PaddyCube/WirelessWeather/Pictures/20190723_202139.jpg

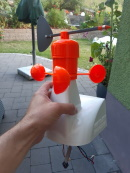
Pictures/20190723_202139.jpg
