PaddyCube/WirelessWeather/Pictures/20190723_202154.jpg

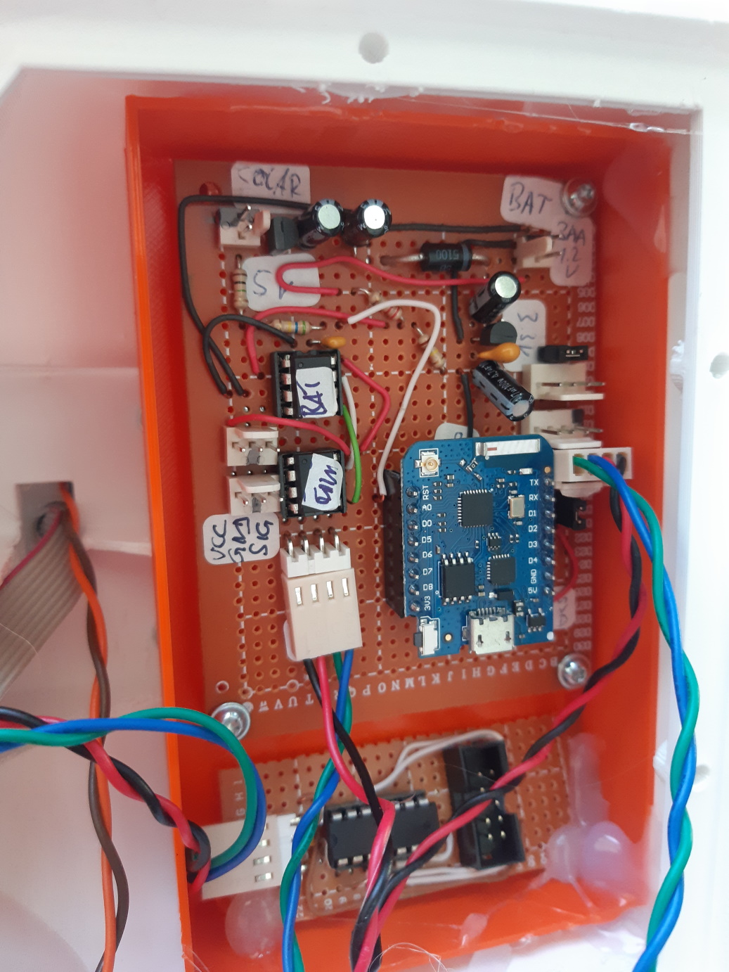
Pictures/20190723_202154.jpg
