PaddyCube/WirelessWeather/Pictures/20190723_202201.jpg

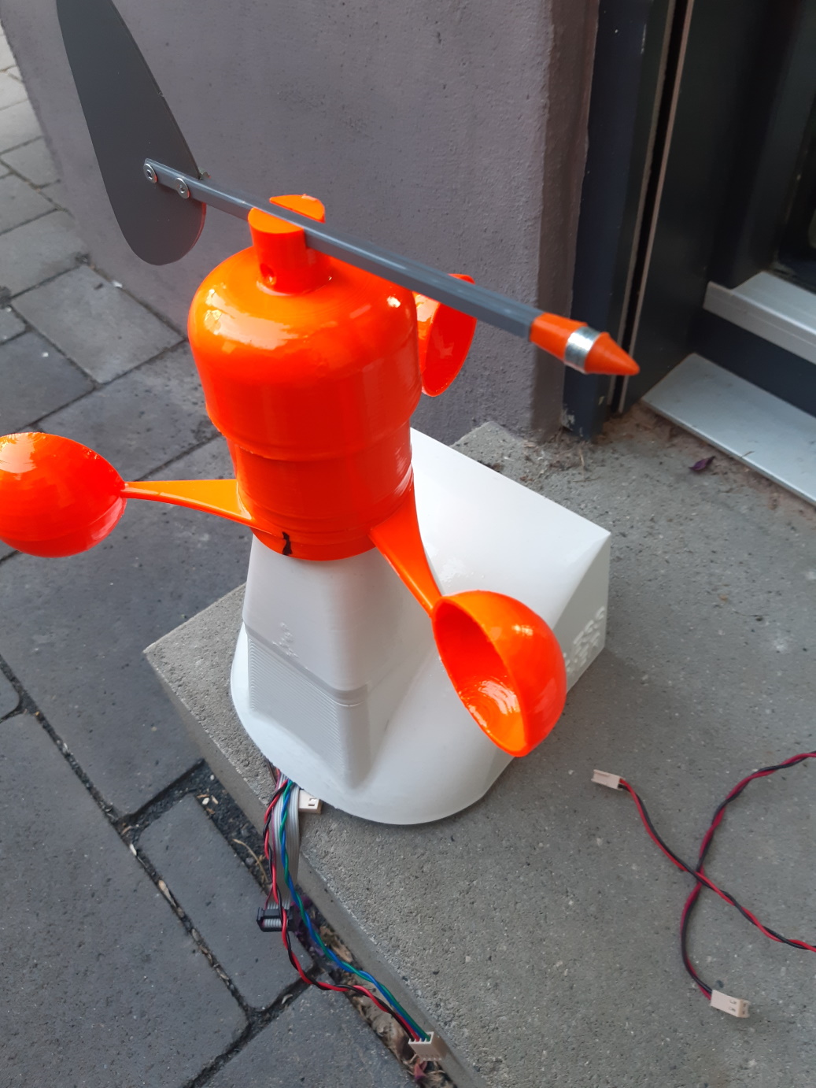
Pictures/20190723_202201.jpg
