PaddyCube/WirelessWeather/Pictures/20190723_202206.jpg

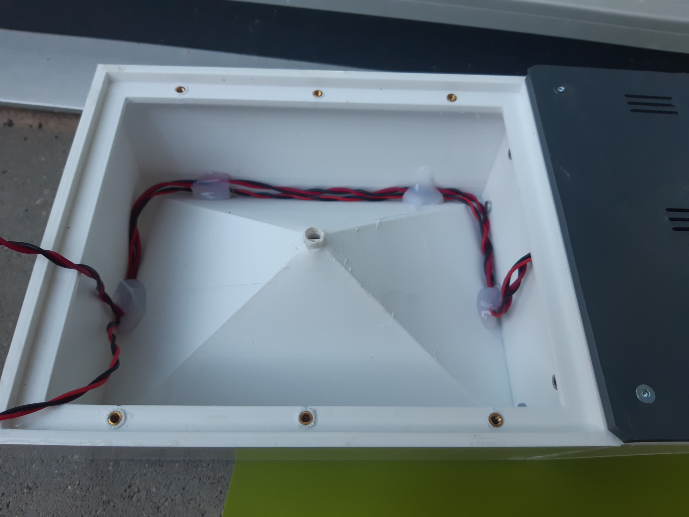
Pictures/20190723_202206.jpg
