PaddyCube/WirelessWeather/Pictures/20190723_202212.jpg

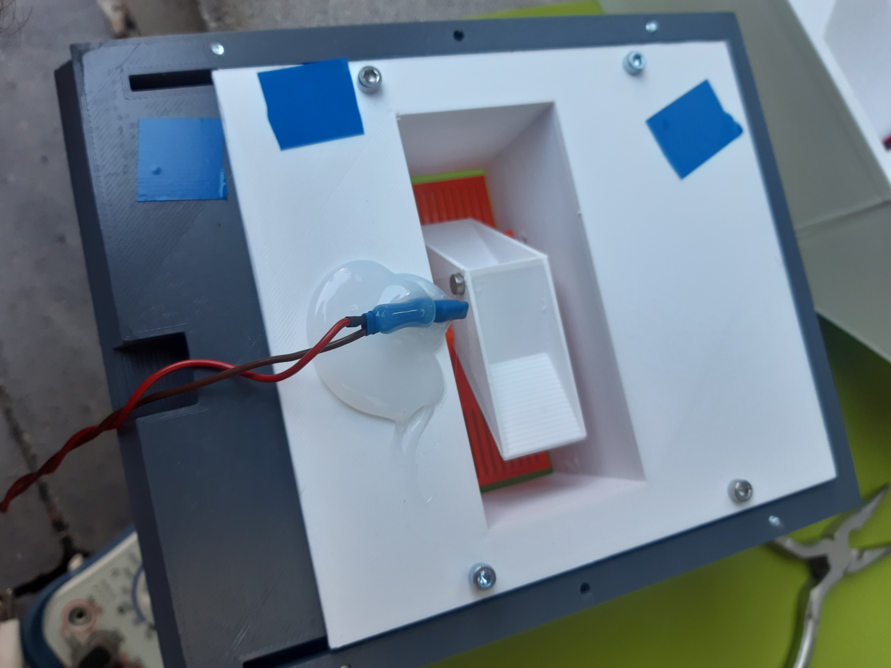
Pictures/20190723_202212.jpg
