PaddyCube/WirelessWeather/Pictures/20190723_202252.jpg

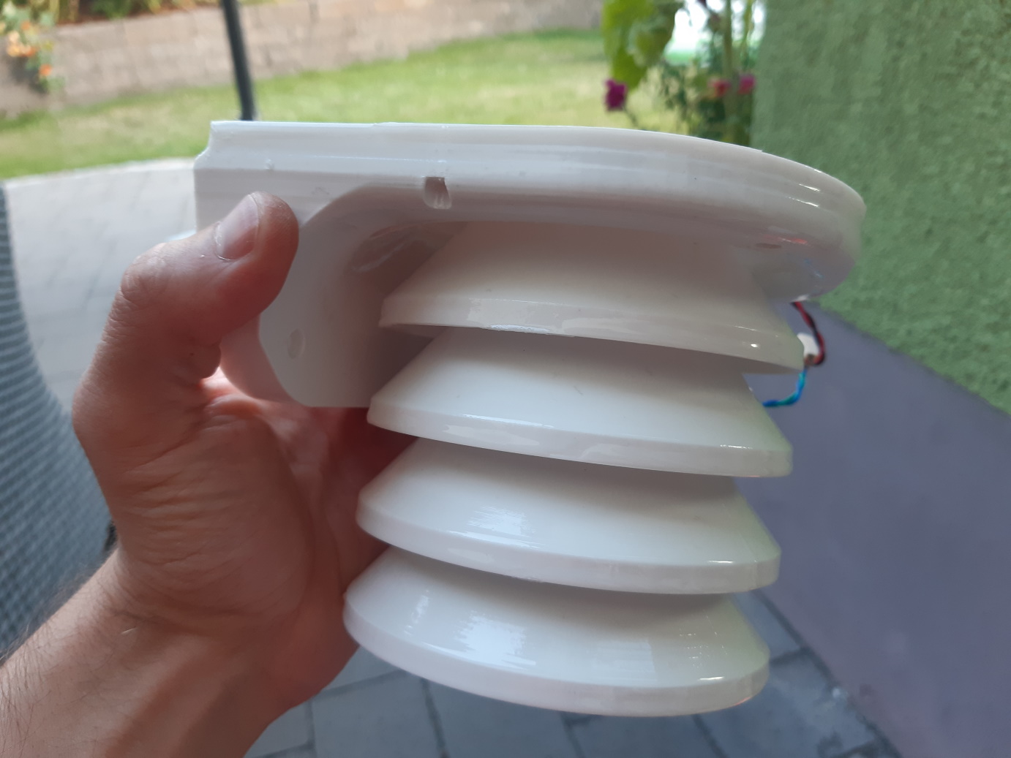
Pictures/20190723_202252.jpg
