PaddyCube/WirelessWeather/Pictures/20190723_202256.jpg

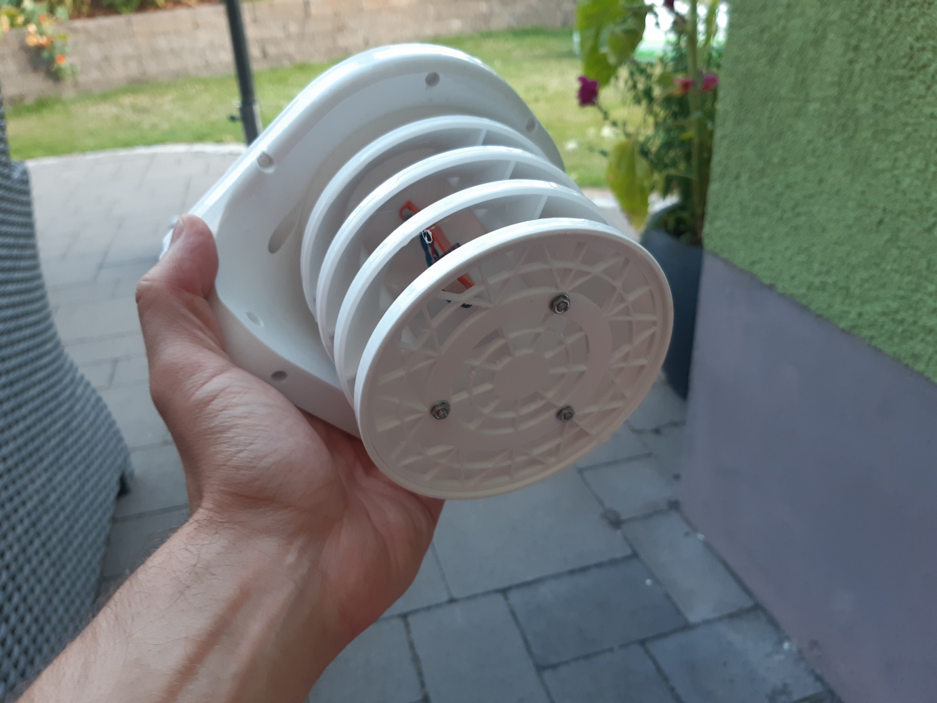
Pictures/20190723_202256.jpg
