PaddyCube/WirelessWeather/Pictures/20190803_131221.jpg

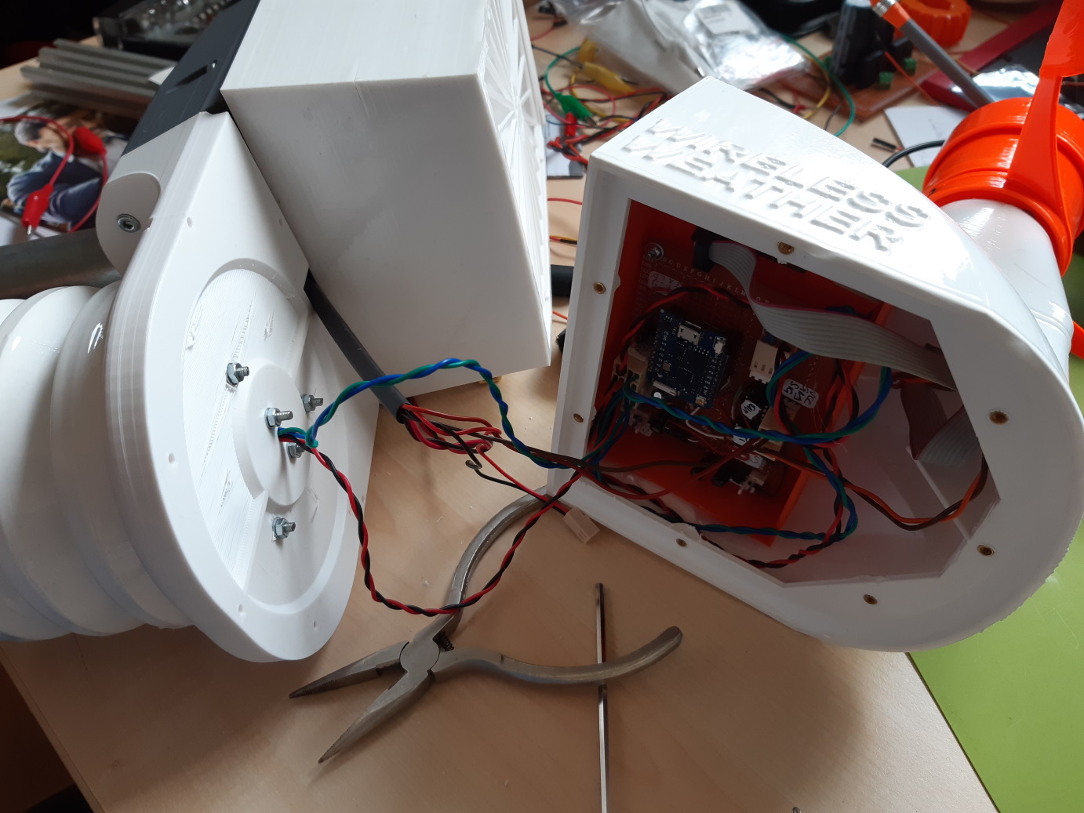
Pictures/20190803_131221.jpg
