PaddyCube/WirelessWeather/Pictures/20190803_132253.jpg

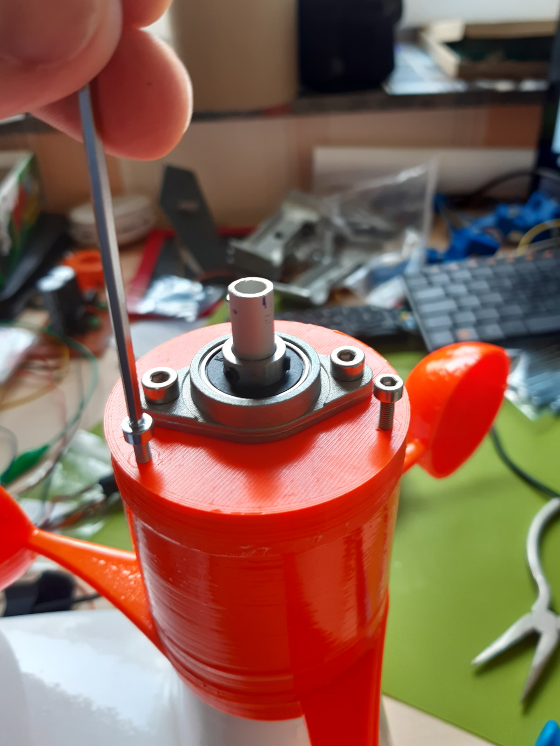
Pictures/20190803_132253.jpg
