PaddyCube/WirelessWeather/Pictures/20190803_132257.jpg

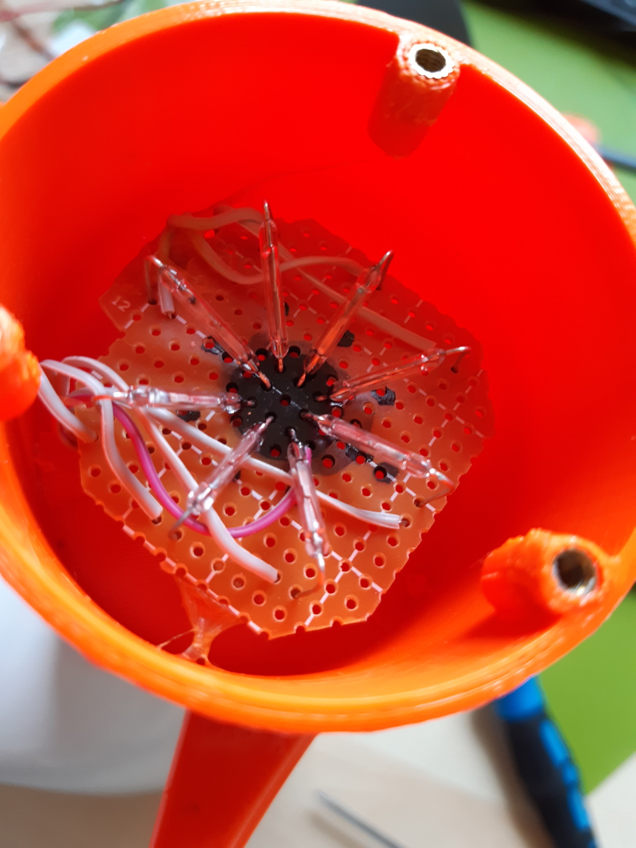
Pictures/20190803_132257.jpg
