PaddyCube/WirelessWeather/Pictures/20190806_172404.jpg

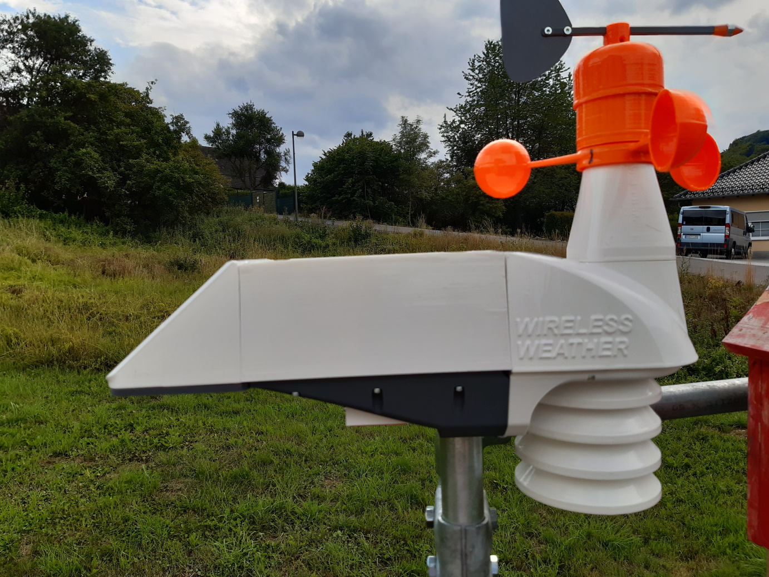
Pictures/20190806_172404.jpg
