PaddyCube/WirelessWeather/Pictures/20190806_172607.jpg

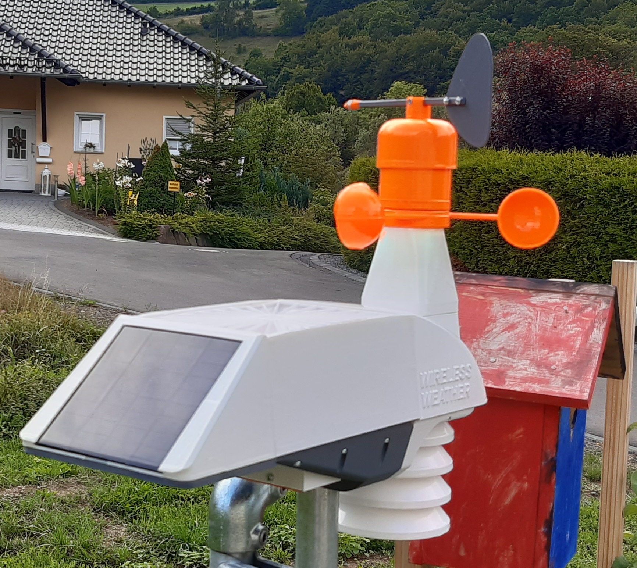
Pictures/20190806_172607.jpg
