PaddyCube/WirelessWeather/STL/schnitt.png

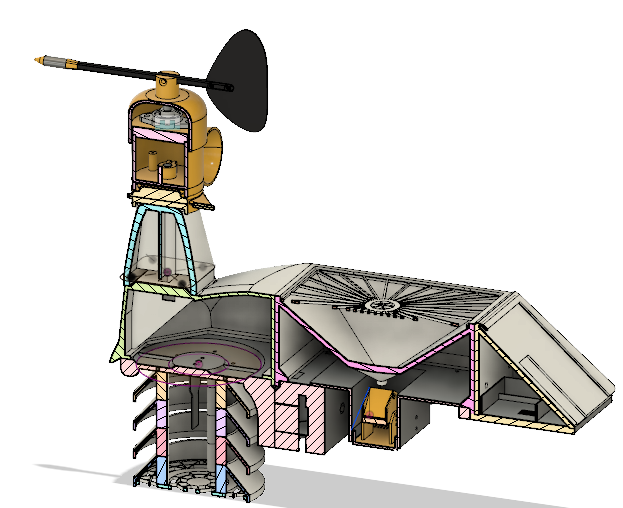
STL/schnitt.png
