PaddyCube/WirelessWeather/STL/seite.png

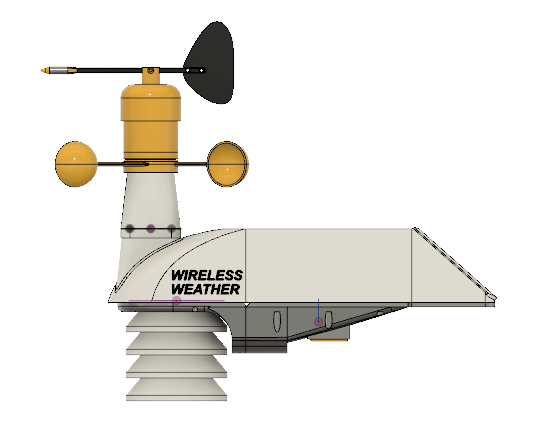
STL/seite.png
