PaddyCube/WirelessWeather/STL/station.png

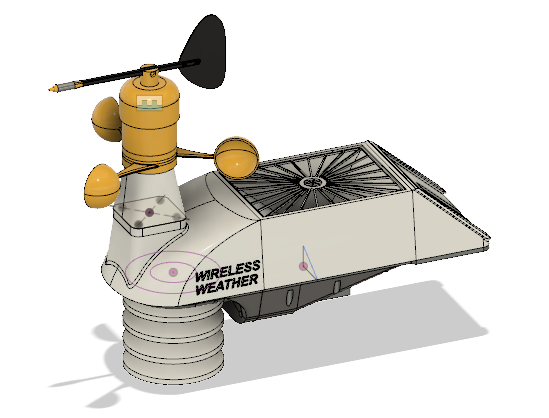
STL/station.png
