PaddyCube/WirelessWeather/STL/unten.png

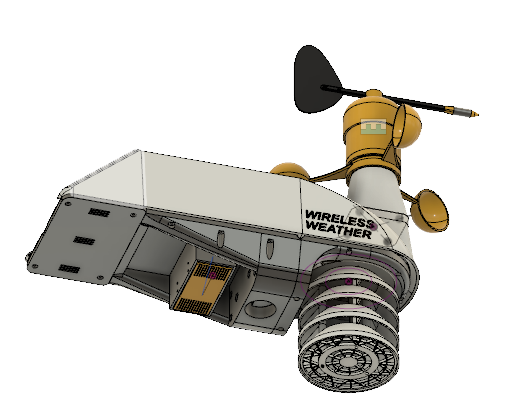
STL/unten.png
