PaddyCube/WirelessWeather/STL/vorne.png

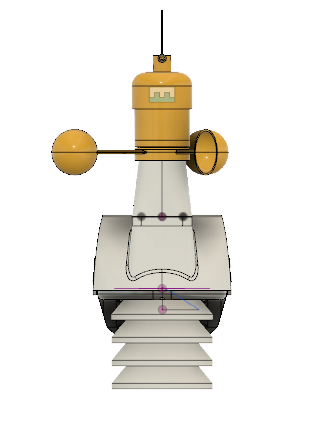
STL/vorne.png
