PaddyCube/WirelessWeather/STL/Anemometer-lower-part v17.stl

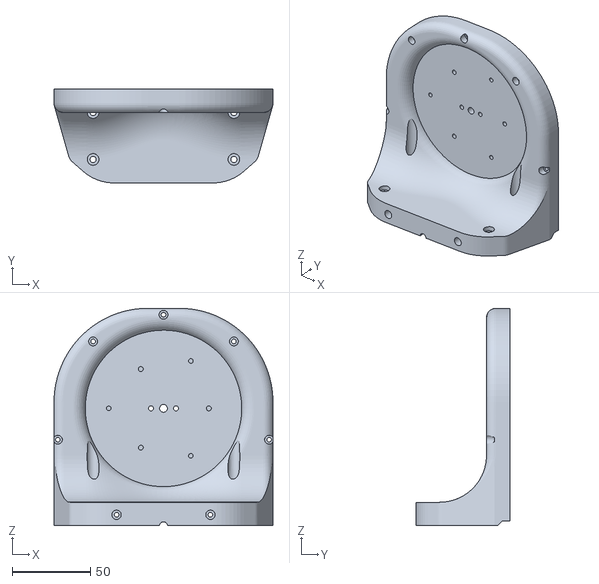
[picture p34: CAD file, 2020-04-20]
STL/Anemometer-lower-part v17.stl
140.0 x 60.0 x 139.0
