PaddyCube/WirelessWeather/STL/Sensor-Mount.stl

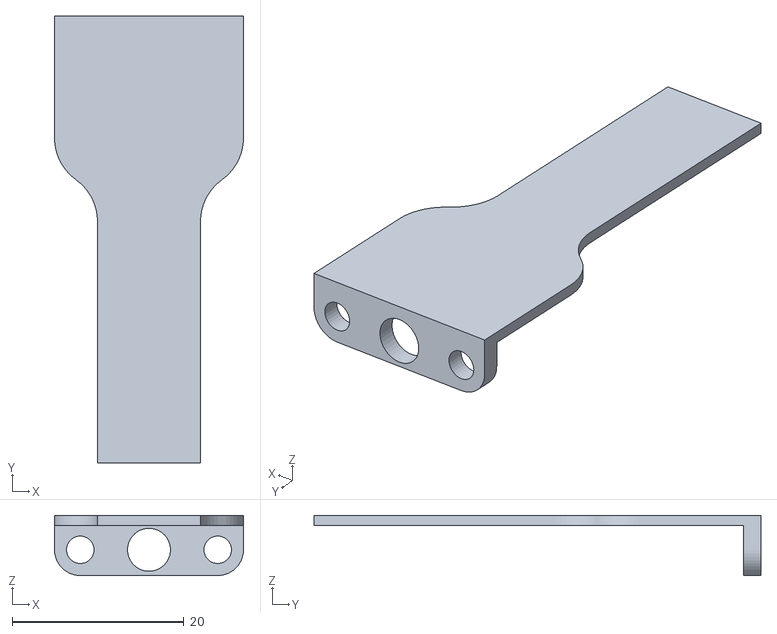
[picture p35: CAD file, 2020-04-20]
STL/Sensor-Mount.stl
22.0 x 52.0 x 7.00
