PaddyCube/WirelessWeather/STL/Rain_Gauge_Cover.stl

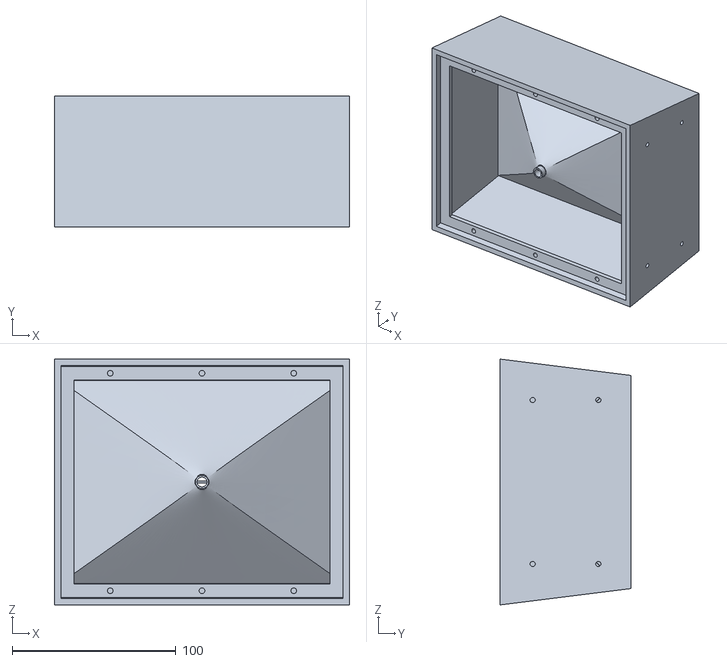
[picture p36: CAD file, 2020-04-20]
STL/Rain_Gauge_Cover.stl
180.0 x 80.0 x 150.0
