PaddyCube/WirelessWeather/STL/Solar-Modul.stl

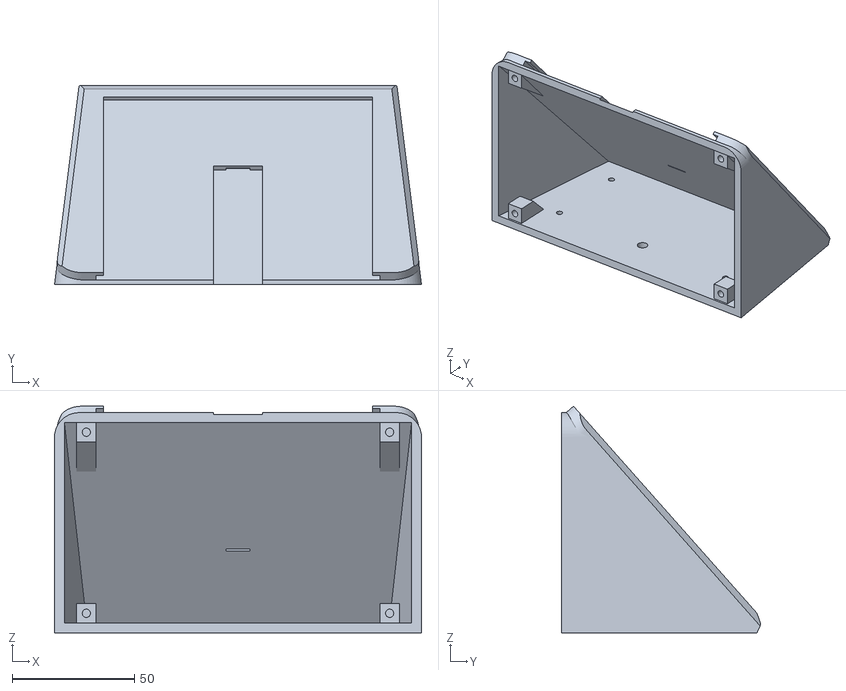
[picture p37: CAD file, 2020-04-20]
STL/Solar-Modul.stl
150.0 x 81.5 x 92.7
