PaddyCube/WirelessWeather/STL/Stevenson-Screen-Mittelteil.stl

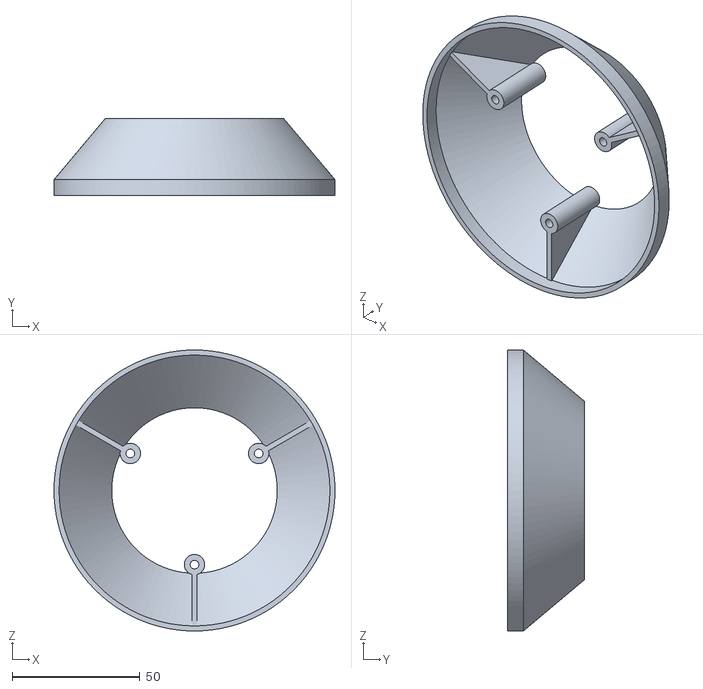
[picture p38: CAD file, 2020-04-20]
STL/Stevenson-Screen-Mittelteil.stl
110.0 x 30.0 x 110.0
