PaddyCube/WirelessWeather/STL/Wetterstation-upper-part.stl

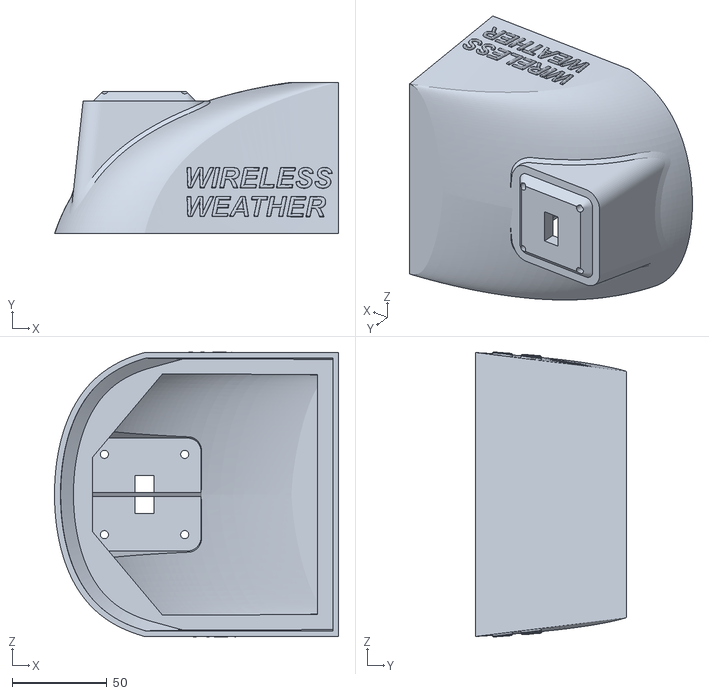
[picture p39: CAD file, 2020-04-20]
STL/Wetterstation-upper-part.stl
150.0 x 80.0 x 150.5
