PaddyCube/WirelessWeather/STL/Windfahne-unten.stl

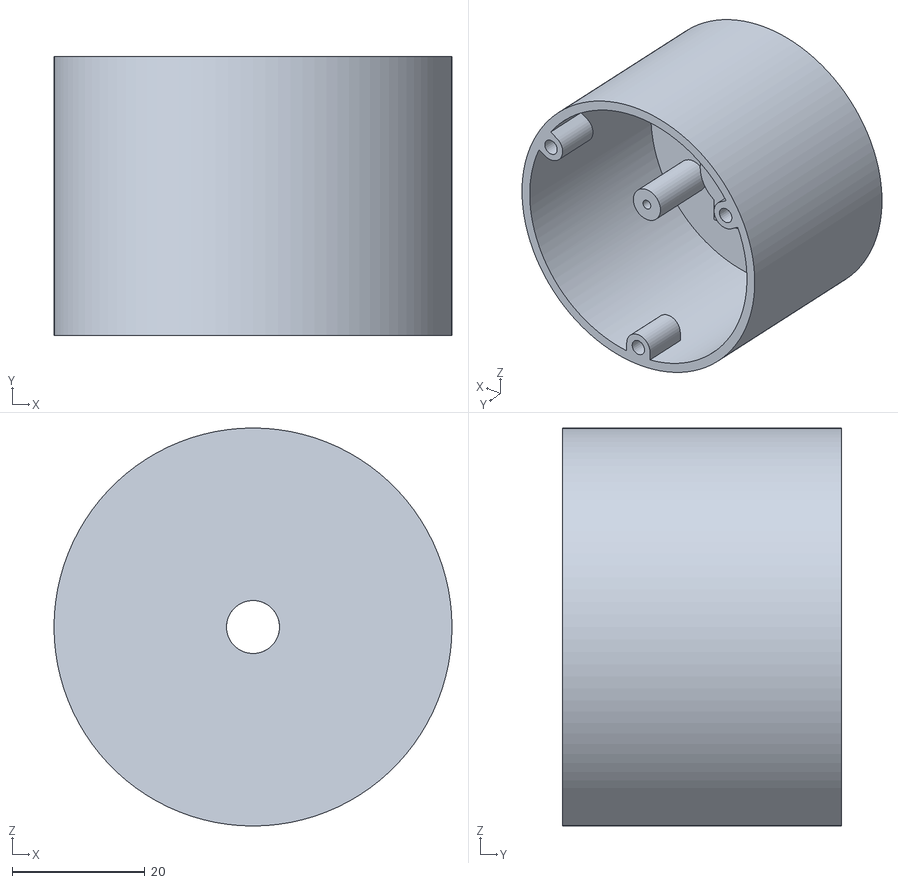
[picture p40: CAD file, 2020-04-20]
STL/Windfahne-unten.stl
60.0 x 42.0 x 60.0
