PaddyCube/WirelessWeather/STL/Windfahne-Balance1.stl

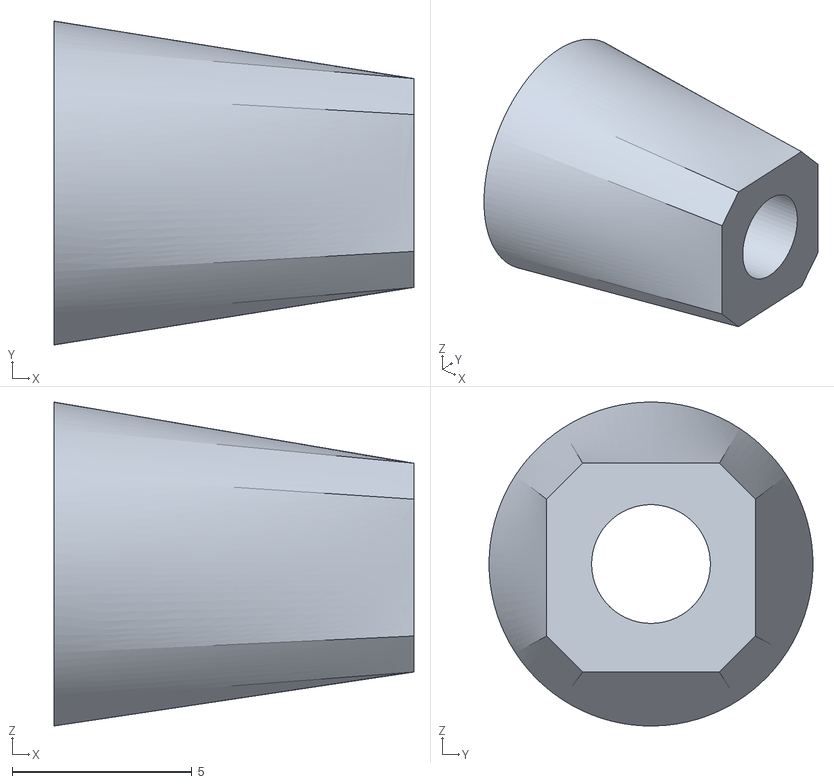
[picture p41: CAD file, 2020-04-20]
STL/Windfahne-Balance1.stl
10.0 x 9.00 x 9.00
