PaddyCube/WirelessWeather/STL/Windfahne-Mast.stl

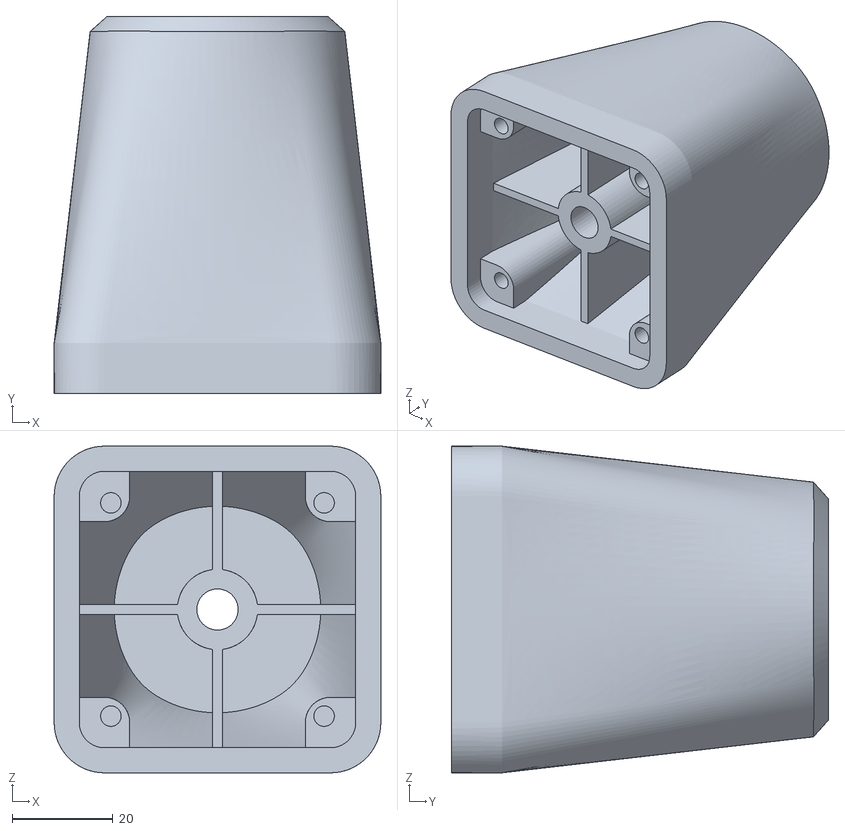
[picture p42: CAD file, 2020-04-20]
STL/Windfahne-Mast.stl
65.0 x 75.0 x 65.0
