PaddyCube/WirelessWeather/STL/Windfahne-Deckel.stl

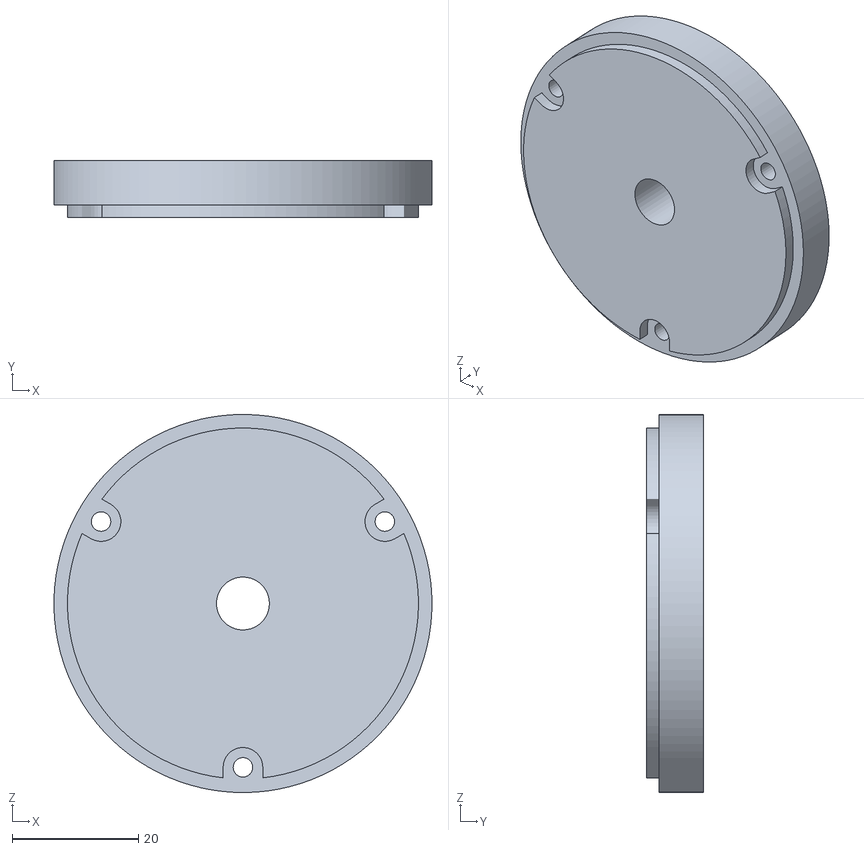
[picture p43: CAD file, 2020-04-20]
STL/Windfahne-Deckel.stl
60.0 x 9.00 x 60.0
