PaddyCube/WirelessWeather/STL/Windfahne-Paddel.stl

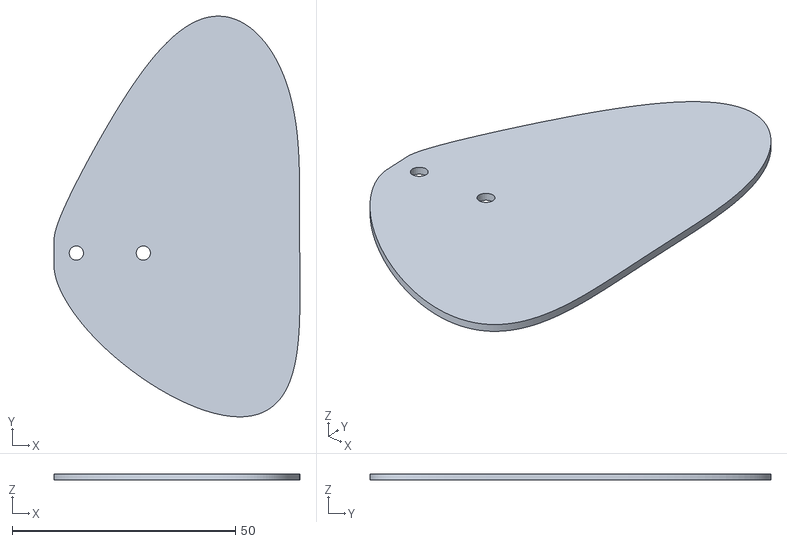
[picture p44: CAD file, 2020-04-20]
STL/Windfahne-Paddel.stl
55.1 x 89.7 x 1.40
