PaddyCube/WirelessWeather/STL/Platinenhalter.stl

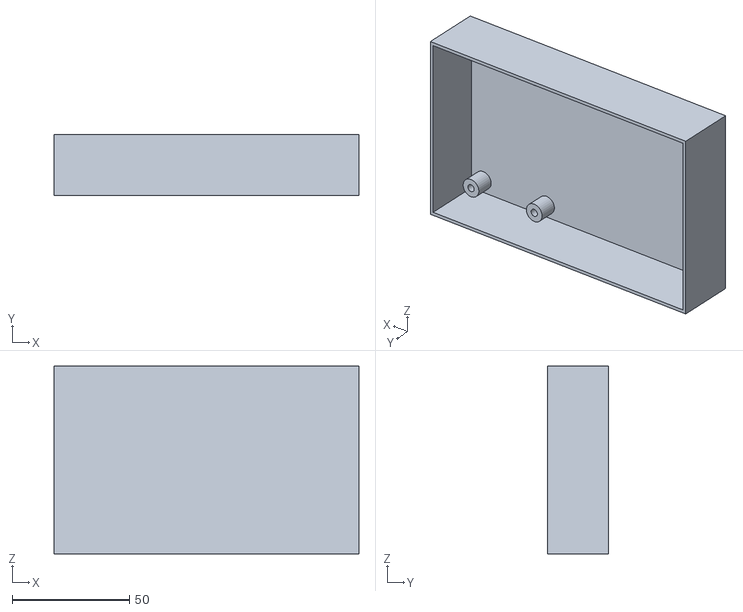
[picture p45: CAD file, 2020-04-20]
STL/Platinenhalter.stl
130.0 x 26.0 x 80.0
