PaddyCube/WirelessWeather/code/ESP32/ESP32_WirelessWeather/ulp_main.h

/*
    Put your ULP globals here you want visibility
    for your sketch. Add "ulp_" to the beginning
    of the variable name and must be size 'uint32_t'
*/
#include "Arduino.h"

extern uint32_t ulp_entry;

extern uint32_t ulp_edge_count_to_wake_up;
extern uint32_t ulp_debounce_max_count;

extern uint32_t ulp_next_edge_wind;
extern uint32_t ulp_debounce_counter_wind;
extern uint32_t ulp_edge_count_wind;
extern uint32_t ulp_io_number_wind;

extern uint32_t ulp_next_edge_rain;
extern uint32_t ulp_debounce_counter_rain;
extern uint32_t ulp_edge_count_rain;
extern uint32_t ulp_io_number_rain;
