PaddyCube/WirelessWeather/code/Arduino Mini/ESP8266WirelessWeatherReceiver/settings.h

#ifndef SETTINGS_H_
#define SETTINGS_H_


// WIFI -settings
const char *SSID = "YOUR SSID";
const char *PSK = "YOUR_PASSWORD";


// MQTT Settings
const char *MQTT_BROKER = "IP of MQTT Broker";
const int MQTT_PORT = 1883;

// Sleep settings for ESP8266
const int SLEEP_MIN = 3;


#endif
